thrushd/tabletop-soundboard/electrical/3d_models/TSSOP-24 0.65p.step

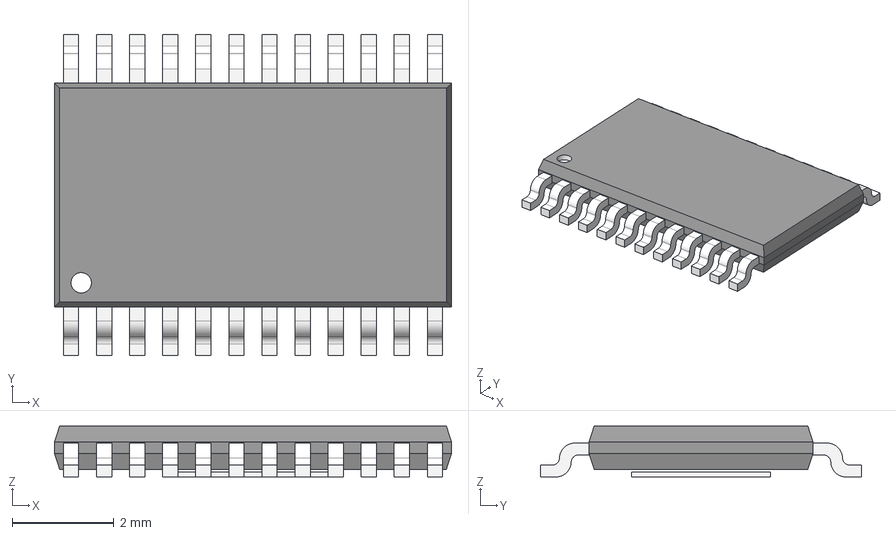
[picture p16: CAD file, 2023-04-10]
electrical/3d_models/TSSOP-24 0.65p.step
7.80 x 6.30 x 1.00 mm
