thrushd/tabletop-soundboard/electrical/3d_models/ER-TFT013-2_loose.stp

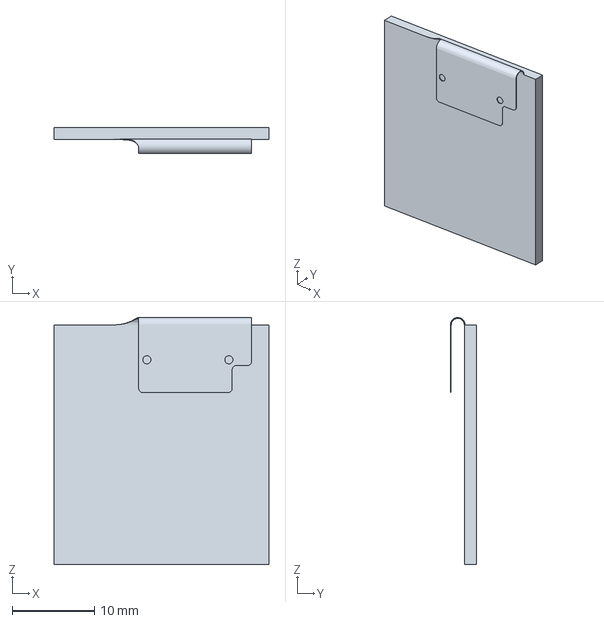
[picture p17: CAD file, 2023-04-10]
electrical/3d_models/ER-TFT013-2_loose.stp
26.2 x 3.20 x 30.1 mm
