thrushd/tabletop-soundboard/electrical/3d_models/PEC12R-4215F-S0024.stp

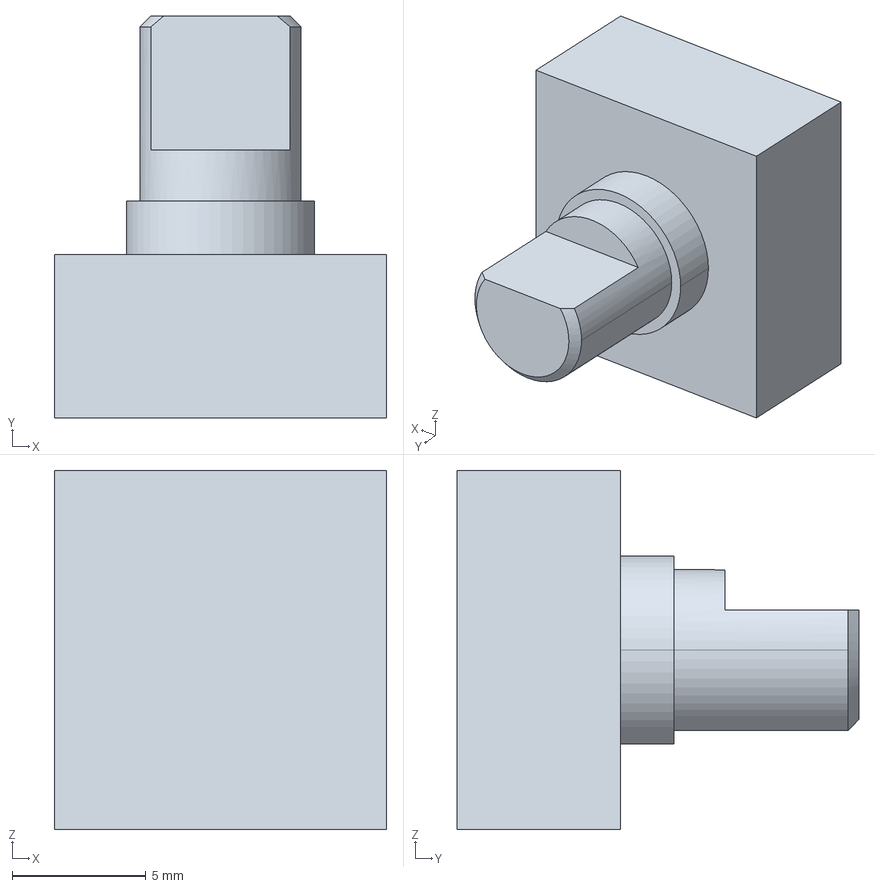
[picture p18: CAD file, 2023-04-10]
electrical/3d_models/PEC12R-4215F-S0024.stp
12.4 x 15.0 x 13.4 mm
