thrushd/tabletop-soundboard/firmware/src/module.h

#pragma once

#include "helper_functions.h"
#include "track.h"
#include <Adafruit_GFX.h>
#include <Adafruit_SSD1306.h>
#include <Arduino.h>
#include <Audio.h>
#include <Encoder.h>
#include <OneButton.h>
#include <Wire.h>

#define MODULE_SCREEN_WIDTH 128 // OLED display width, in pixels
#define MODULE_SCREEN_HEIGHT 32 // OLED display height, in pixels
#define OLED_RESET -1
#define SCREEN_ADDRESS 0x3C
#define GAIN_MIN 0
#define GAIN_MAX 1

#define TCA_ADDR 0x70 // address of i2c multiplexer chip

class Module {
public:
    Module(int module_number, int button_pin, AudioPlaySdWav* play_sd, AudioMixer4* mixer_left, AudioMixer4* mixer_right, TwoWire* twi, Encoder* knob);
    void update(int new_scene_index);
    void init(Track** tracks_in);
    void stop();
    // module button, public so we can see if it's being held down
    OneButton button;
private:
    // pointer to array of track objects
    Track** tracks;
    int scene_index = -1;
    int module_number;
    bool skip = false;
    // audio
    AudioPlaySdWav* play_sd;
    AudioMixer4* mixer_left;
    AudioMixer4* mixer_right;
    int mixer_channel_number;
    bool play_flag = false;
    bool loop_flag = false;
    uint32_t track_duration;
    // display
    Adafruit_SSD1306 display;
    TwoWire* twi;
    // button
    int button_pin;
    // encoder knob for main display
    Encoder* knob;
    long old_position = 0;
    long new_position = 0;
    double gain_diff = 0;
    int enc_int_min = 0;
    int enc_int_max = 80; // 4 counts per detent showing on 0.05 scale 4*20

    // functions
    // void init();
    // LCD stuff
    void set_mp_addr();
    void update_display();
    void display_empty();
    void display_file_not_found();
    // audio stuff
    static void handle_single(void* ptr);
    static void handle_double(void* ptr);
    static void handle_hold(void* ptr);

    void process_single();
    void process_double();
    void process_hold();

    String millis_to_hhmmss(uint32_t time_millis);

    void rect_progress_bar(uint16_t x, uint16_t y, uint16_t w, uint16_t h, uint32_t progress, uint32_t duration);
    void volume_display(uint16_t x, uint16_t y, uint16_t w, uint16_t h, double gain, double max);
};
